Daft-Freak/gba-cart-read/config.h

#pragma once
// these are the defaults

#ifndef USB_VENDOR_ID
#define USB_VENDOR_ID 0xCafe
#endif

#ifndef USB_VENDOR_STR
#define USB_VENDOR_STR "TinyUSB"
#endif

#ifndef USB_PRODUCT_STR
#define USB_PRODUCT_STR "Device"
#endif
