Daft-Freak/gba-cart-read/filesystem.hpp

#pragma once

#include <cstdint>

namespace Filesystem
{
    using ReadFunc = void(*)(uint32_t offset, uint32_t len, uint8_t *buf);

    void setTargetSize(uint32_t size);
    uint32_t getNumSectors();

    void setVolumeLabel(const char *label);

    void addFile(uint32_t offset, uint32_t size, const char *shortName, const char *shortExt, ReadFunc readFn, const char *longName = nullptr);
    void addFile(uint32_t offset, uint32_t size, const char *longName, ReadFunc readFn);
    void resetFiles();

    void read(uint32_t sector, uint32_t count, uint8_t *buf);
}
